hanyazou/Nucleo64_Z80-H533/FW/src/nucleo64_z80/disk_file.c

/*
 * Copyright (c) 2023-2026 @hanyazou
 *
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
 * THE SOFTWARE IS PROVIDED "AS IS", WITHOUT WARRANTY OF ANY KIND,
 * EXPRESS OR IMPLIED, INCLUDING BUT NOT LIMITED TO THE WARRANTIES OF
 * MERCHANTABILITY, FITNESS FOR A PARTICULAR PURPOSE AND
 * NONINFRINGEMENT. IN NO EVENT SHALL THE AUTHORS OR COPYRIGHT HOLDERS BE
 * LIABLE FOR ANY CLAIM, DAMAGES OR OTHER LIABILITY, WHETHER IN AN ACTION
 * OF CONTRACT, TORT OR OTHERWISE, ARISING FROM, OUT OF OR IN CONNECTION
 * WITH THE SOFTWARE OR THE USE OR OTHER DEALINGS IN THE SOFTWARE.
 */

#include "disk_file.h"
#include "nucleo64_z80.h"
#include "z80_pins.h"

#include <fatfs/fatfs.h>

#include <stdio.h>


static struct drive {
    FIL *filep;
} drives[16] = { };
static const int num_drives = (sizeof(drives)/sizeof(*drives));

#define NUM_FILES 9
static FIL files[NUM_FILES];
static uint16_t file_available = (1 << NUM_FILES) - 1;

static void file_select(void);

void disk_file_init(void)
{
    MX_FATFS_Init();

    struct z80_pin_state pin_state;
    z80_release_pins(&pin_state);
    sd_spi_acquire();

    file_select();

    sd_spi_release();
    z80_acquire_pins(&pin_state);
}

FIL *get_file(void)
{
    for (int i = 0; i < NUM_FILES; i++) {
        if (file_available & (1L << i)) {
            file_available &= ~(1L << i);
            // printf("%s: allocate %d, available=%04x\r\n", __func__, i, file_available);
            return &files[i];
        }
    }

    return NULL;
}

void put_file(FIL *file)
{
    for (int i = 0; i < NUM_FILES; i++) {
        if (file == &files[i]) {
            assert(!(file_available & (1L << i)));
            file_available |= (1L << i);
            return ;
        }
    }
}

bool disk_file_have_boot_disk(void)
{
    return (drives[0].filep != NULL);
}

static void file_select(void)
{
    int i;
    unsigned int drive;
    static FATFS FatFs;	//Fatfs handle
    FRESULT fres; //Result after operations
    DIR fsdir;
    FILINFO fileinfo;

    //Open the file system
    fres = f_mount(&FatFs, "", 1); //1=mount now
    if (fres != FR_OK) {
        printf("Failed to mount SD Card (%i)\r\n", fres);
        return;
    }

    //
    // Select disk image folder
    //
    fres = f_opendir(&fsdir, "/");
    if (fres  != FR_OK) {
        printf("Failed to open SD Card (%i)\r\n", fres);
    }

    i = 0;
    int selection = -1;
    int preferred = -1;
    f_rewinddir(&fsdir);
    while (f_readdir(&fsdir, &fileinfo) == FR_OK && fileinfo.fname[0] != 0) {
        if (strncmp(fileinfo.fname, "CPMDISKS", 8) == 0 ||
            strncmp(fileinfo.fname, "CPMDIS~", 7) == 0) {
            printf("%d: %s\r\n", i, fileinfo.fname);
            if (strcmp(fileinfo.fname, "CPMDISKS") == 0) {
                selection = i;
            }
            i++;
        }
    }
    if (0 <= preferred) {
        selection = preferred;
    }
    printf("B: ROM BASIC\r\n");
    if (1 < i) {
        if (0 <= selection) {
            printf("Select[%d]: ", selection);
        } else {
            printf("Select: ");
        }
        while (1) {
            uint8_t c = (uint8_t)getchar();  // Wait for input char
            if ('0' <= c && c <= '9' && c - '0' < i) {
                selection = c - '0';
                break;
            }
            if (c == 'b' || c == 'B') {
                printf("B\r\n");
                return;
            }
            if ((c == 0x0d || c == 0x0a) && 0 <= selection)
                break;
        }
        printf("%d\r\n", selection);
        f_rewinddir(&fsdir);
        i = 0;
        while (f_readdir(&fsdir, &fileinfo) == FR_OK && fileinfo.fname[0] != 0) {
            if (strncmp(fileinfo.fname, "CPMDISKS", 8) == 0 ||
                strncmp(fileinfo.fname, "CPMDIS~", 7) == 0) {
                if (selection == i)
                    break;
                i++;
            }
        }
        printf("%s is selected.\r\n", fileinfo.fname);
    } else {
        strcpy(fileinfo.fname, "CPMDISKS");
    }
    f_closedir(&fsdir);

    //
    // Open disk images
    //
    char buf[26];
    for (drive = 0; drive < num_drives; drive++) {
        char drive_letter = (char)('A' + drive);
        sprintf(buf, "%s/DRIVE%c.DSK", fileinfo.fname, drive_letter);
        if (f_stat(buf, NULL) != FR_OK) {
            sprintf(buf, "CPMDISKS.CMN/DRIVE%c.DSK", drive_letter);
            if (f_stat(buf, NULL) != FR_OK) {
                continue;
            }
        }
        FIL *filep = get_file();
        if (filep == NULL) {
            printf("Too many files\r\n");
            break;
        }
        if (f_open(filep, buf, FA_READ|FA_WRITE) == FR_OK) {
            printf("Image file %s is assigned to drive %c\r\n", buf, drive_letter);
            drives[drive].filep = filep;
        }
    }
    if (!disk_file_have_boot_disk()) {
        printf("No boot disk.\r\n");
        return;
    }

    return;
}

bool disk_file_read(uint8_t drive, uint32_t offs, uint8_t *buf, int buf_len) {
    FIL *filep = drives[drive].filep;
    unsigned int n;
    FRESULT fres;
    if (filep == NULL) {
        printf("%s: drive=%u: no disk\r\n", __func__, drive);
        return false;
    }
    if ((fres = f_lseek(filep, offs)) != FR_OK) {
        printf("%s: drive=%u: f_lseek(): ERROR %d\r\n", __func__, drive, fres);
        return false;
    }
    if ((fres = f_read(filep, buf, buf_len, &n)) != FR_OK || n != buf_len) {
        printf("%s: drive=%u: f_read(): ERROR res=%d, n=%d\r\n", __func__, drive, fres, n);
        return false;
    }
    return true;
}

bool disk_file_write(uint8_t drive, uint32_t offs, uint8_t *buf, int buf_len) {
    FIL *filep = drives[drive].filep;
    unsigned int n;
    FRESULT fres;
    if (filep == NULL) {
        printf("%s: drive=%u: no disk\r\n", __func__, drive);
        return false;
    }
    if ((fres = f_lseek(filep, offs)) != FR_OK) {
        printf("%s: drive=%u: f_lseek(): ERROR %d\r\n", __func__, drive, fres);
        return false;
    }
    if ((fres = f_write(filep, buf, buf_len, &n)) != FR_OK || n != buf_len) {
        printf("%s: drive=%u: f_read(): ERROR res=%d, n=%d\r\n", __func__, drive, fres, n);
        return false;
    }
    if ((fres = f_sync(filep)) != FR_OK) {
        printf("%s: drive=%u: f_sync(): ERROR %d\r\n", __func__, drive, fres);
        return false;
    }
    return true;
}
