hanyazou/Nucleo64_Z80-H533/FW/projects/h503_board_test/Core/Src/main.c

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
/* Includes ------------------------------------------------------------------*/
#include "main.h"

/* USER CODE BEGIN Includes */
#include "board_test.h"

#include <stdio.h>

/* USER CODE END Includes */

TIM_HandleTypeDef htim1;
TIM_HandleTypeDef htim5;

UART_HandleTypeDef huart2;

void SystemClock_Config(void);
static void MX_GPIO_Init(void);
static void MX_USART2_UART_Init(void);
static void MX_TIM5_Init(void);
static void MX_TIM1_Init(void);
/**
  * @brief  The application entry point.
  * @retval int
  */
int main(void)
{

  /* MCU Configuration--------------------------------------------------------*/

  /* Reset of all peripherals, Initializes the Flash interface and the Systick. */
  HAL_Init();

  /* Configure the system clock */
  SystemClock_Config();

  /* Initialize all configured peripherals */
  MX_GPIO_Init();
  MX_USART2_UART_Init();
  MX_TIM5_Init();
  MX_TIM1_Init();
  /* USER CODE BEGIN 2 */
  HAL_TIM_PWM_Start(&htim5, TIM_CHANNEL_1);
  HAL_TIM_Base_Start(&htim1);

  //disable buffering for input/output stream
  setvbuf(stdin, NULL, _IONBF, 0);
  setvbuf(stdout, NULL, _IONBF, 0);
  board_test();

  /* USER CODE END 2 */

  /* Infinite loop */
  /* USER CODE BEGIN WHILE */
  while (1)
  {
    /* USER CODE END WHILE */

    /* USER CODE BEGIN 3 */
    static unsigned short pin_state = 0;
    pin_state = !pin_state;
    HAL_GPIO_WritePin(SPI1_SS_GPIO_Port, SPI1_SS_Pin, pin_state);

    printf("Hello, World !!!\r\n");
    HAL_Delay(1000);
  }
  /* USER CODE END 3 */
}

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
/* USER CODE BEGIN 4 */

/**
  * @brief  Retargets the C library printf function to the USART.
  * @param  None
  * @retval None
  */
#ifdef __GNUC__
/* With GCC/RAISONANCE, small printf (option LD Linker->Libraries->Small printf
   set to 'Yes') calls __io_putchar() */
int __io_putchar(int ch)
#else
int fputc(int ch, FILE *f)
#endif /* __GNUC__ */
{
  /* Place your implementation of fputc here */
  /* e.g. write a character to the USART1 and Loop until the end of transmission */
  HAL_UART_Transmit(&huart2, (uint8_t *)&ch, 1, 0xFFFF);

  return ch;
}

#ifdef __GNUC__
int __io_getchar(void)
#else
int fgetc(FILE *f)
#endif
{
  uint8_t ch = 0;
  HAL_StatusTypeDef stat;
  do {
    __HAL_UART_CLEAR_OREFLAG(&huart2);
    stat = HAL_UART_Receive(&huart2, (uint8_t *)&ch, 1, /* Timeout */ 0);
  } while (ch == 0 || stat != HAL_OK);
  return ch;
}

int input_key_available(void)
{
    return __HAL_UART_GET_FLAG(&huart2, UART_FLAG_RXNE);
}

void delay_us (uint16_t us)
{
	__HAL_TIM_SET_COUNTER(&htim1,0);  // set the counter value a 0
	while (__HAL_TIM_GET_COUNTER(&htim1) < us * 8 + 1);  // wait for the counter to reach the us input in the parameter
}

/* USER CODE END 4 */
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
