hanyazou/Nucleo64_Z80-H533/FW/projects/h533_usb_host_test/AZURE_RTOS/App/app_azure_rtos.c

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

/* Includes ------------------------------------------------------------------*/
#include "app_azure_rtos.h"
/* USER CODE BEGIN Includes */
#include "main.h"
#include "ux_api.h"
#include "ux_hcd_stm32.h"

#include <stdio.h>

/* USER CODE END Includes */

#if (USE_STATIC_ALLOCATION == 1)

#if defined ( __ICCARM__ )
#pragma data_alignment=4
#endif
__ALIGN_BEGIN static UCHAR tx_byte_pool_buffer[TX_APP_MEM_POOL_SIZE] __ALIGN_END;
static TX_BYTE_POOL tx_app_byte_pool;

#if defined ( __ICCARM__ )
#pragma data_alignment=4
#endif
__ALIGN_BEGIN static UCHAR  fx_byte_pool_buffer[FX_APP_MEM_POOL_SIZE] __ALIGN_END;
static TX_BYTE_POOL fx_app_byte_pool;

#if defined ( __ICCARM__ )
#pragma data_alignment=4
#endif
__ALIGN_BEGIN static UCHAR  ux_host_byte_pool_buffer[UX_HOST_APP_MEM_POOL_SIZE] __ALIGN_END;
static TX_BYTE_POOL ux_host_app_byte_pool;

#endif

/**
  * @brief  Define the initial system.
  * @param  first_unused_memory : Pointer to the first unused memory
  * @retval None
  */
VOID tx_application_define(VOID *first_unused_memory)
{
  /* USER CODE BEGIN  tx_application_define_1*/

  /* USER CODE END  tx_application_define_1 */
#if (USE_STATIC_ALLOCATION == 1)
  UINT status = TX_SUCCESS;
  VOID *memory_ptr;

  if (tx_byte_pool_create(&tx_app_byte_pool, "Tx App memory pool", tx_byte_pool_buffer, TX_APP_MEM_POOL_SIZE) != TX_SUCCESS)
  {
  }
  else
  {
    memory_ptr = (VOID *)&tx_app_byte_pool;
    status = App_ThreadX_Init(memory_ptr);
    if (status != TX_SUCCESS)
    {
      /* USER CODE BEGIN  App_ThreadX_Init_Error */
      while(1)
      {
      }
      /* USER CODE END  App_ThreadX_Init_Error */
    }
  }
  if (tx_byte_pool_create(&fx_app_byte_pool, "Fx App memory pool", fx_byte_pool_buffer, FX_APP_MEM_POOL_SIZE) != TX_SUCCESS)
  {
  }
  else
  {
    memory_ptr = (VOID *)&fx_app_byte_pool;
    status = MX_FileX_Init(memory_ptr);
    if (status != FX_SUCCESS)
    {
      /* USER CODE BEGIN  MX_FileX_Init_Error */
      while(1)
      {
      }
      /* USER CODE END  MX_FileX_Init_Error */
    }
  }

  if (tx_byte_pool_create(&ux_host_app_byte_pool, "Ux App memory pool", ux_host_byte_pool_buffer, UX_HOST_APP_MEM_POOL_SIZE) != TX_SUCCESS)
  {
   }
  else
  {
    memory_ptr = (VOID *)&ux_host_app_byte_pool;
    status = MX_USBX_Host_Init(memory_ptr);
    if (status != UX_SUCCESS)
    {
      /* USER CODE BEGIN  MX_USBX_Host_Init_Error */
      while(1)
      {
      }
      /* USER CODE END  MX_USBX_Host_Init_Error */
    }
    /* USER CODE BEGIN  MX_USBX_Host_Init_Success */
    UINT status = ux_host_stack_hcd_register(
      (UCHAR *)"HCD_FS",
      ux_hcd_stm32_initialize,
      USB_DRD_FS,
      (ULONG)&hhcd_USB_DRD_FS);
    if (status != UX_SUCCESS) {
      printf("ux_host_stack_hcd_register() failed\r\n");
      Error_Handler();
    }
    if (HAL_HCD_Start(&hhcd_USB_DRD_FS) != HAL_OK) {
      printf("HAL_HCD_Start() failed\r\n");
      Error_Handler();
    }
    printf("HAL_HCD_Start() succeeded\r\n");

    /* USER CODE END  MX_USBX_Host_Init_Success */

  }

#else
/*
 * Using dynamic memory allocation requires to apply some changes to the linker file.
 * ThreadX needs to pass a pointer to the first free memory location in RAM to the tx_application_define() function,
 * using the "first_unused_memory" argument.
 * This require changes in the linker files to expose this memory location.
 * For EWARM add the following section into the .icf file:
     place in RAM_region    { last section FREE_MEM };
 * For MDK-ARM
     - either define the RW_IRAM1 region in the ".sct" file
     - or modify the line below in "tx_initialize_low_level.S to match the memory region being used
        LDR r1, =|Image$$RW_IRAM1$$ZI$$Limit|

 * For STM32CubeIDE add the following section into the .ld file:
     ._threadx_heap :
       {
          . = ALIGN(8);
          __RAM_segment_used_end__ = .;
          . = . + 64K;
          . = ALIGN(8);
        } >RAM_D1 AT> RAM_D1
    * The simplest way to provide memory for ThreadX is to define a new section, see ._threadx_heap above.
    * In the example above the ThreadX heap size is set to 64KBytes.
    * The ._threadx_heap must be located between the .bss and the ._user_heap_stack sections in the linker script.
    * Caution: Make sure that ThreadX does not need more than the provided heap memory (64KBytes in this example).
    * Read more in STM32CubeIDE User Guide, chapter: "Linker script".

 * The "tx_initialize_low_level.S" should be also modified to enable the "USE_DYNAMIC_MEMORY_ALLOCATION" flag.
 */

  /* USER CODE BEGIN DYNAMIC_MEM_ALLOC */
  (void)first_unused_memory;
  /* USER CODE END DYNAMIC_MEM_ALLOC */
#endif

}
