hanyazou/Nucleo64_Z80-H533/FW/projects/h503_board_test/Core/Inc/board_test.h

/*
 * board_test.h
 *
 *  Created on: Mar 25, 2024
 *      Author: hanyazou
 */

#ifndef INC_BOARD_TEST_H_
#define INC_BOARD_TEST_H_

#include <stdint.h>

extern void board_test(void);

#endif /* INC_BOARD_TEST_H_ */
